rkhamilton/uAlarm/diptrace/uAlarm-audio-PCB.jpg

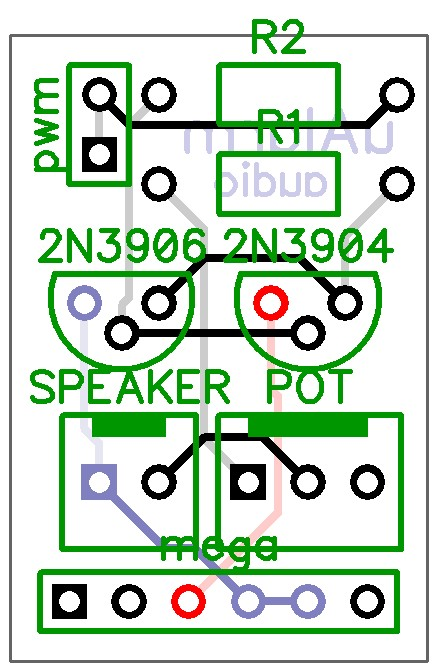
diptrace/uAlarm-audio-PCB.jpg
