rkhamilton/uAlarm/images/glue-detail.jpg

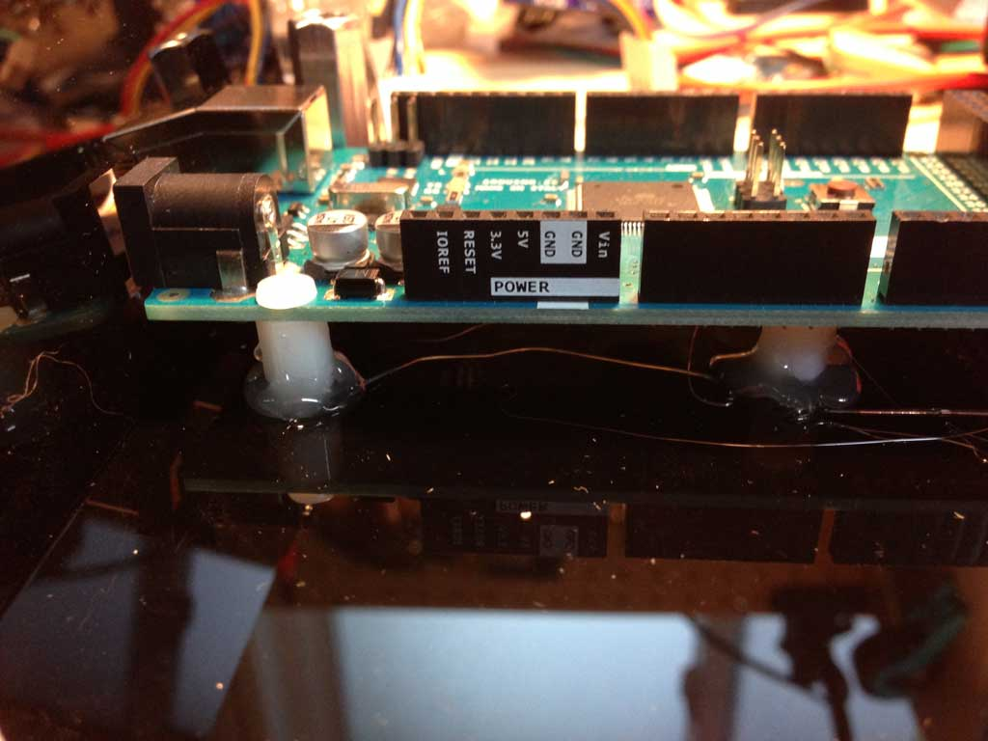
images/glue-detail.jpg
