rkhamilton/uAlarm/images/ponoko-p2.jpg

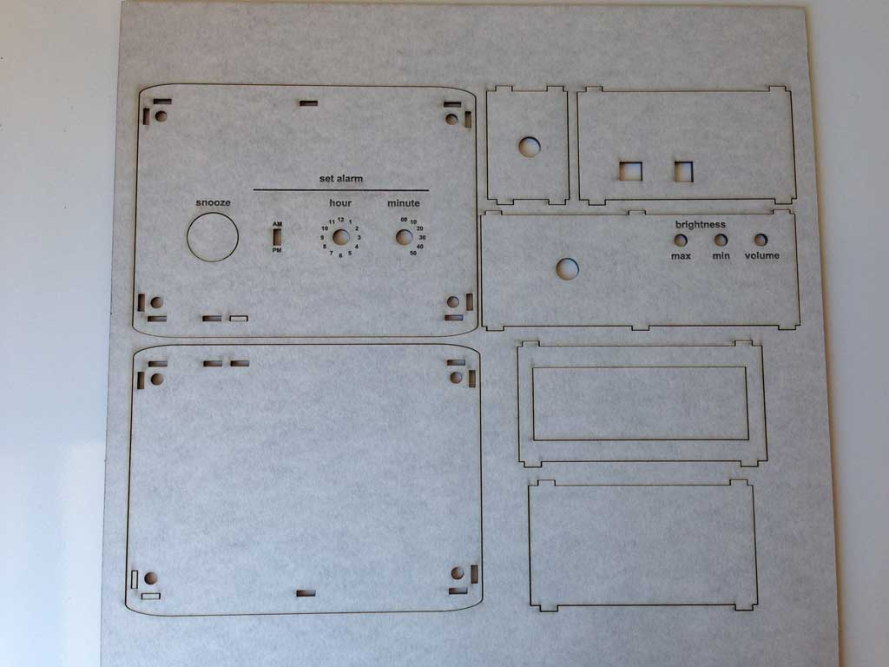
images/ponoko-p2.jpg
