rkhamilton/uAlarm/images/top-angle.jpg

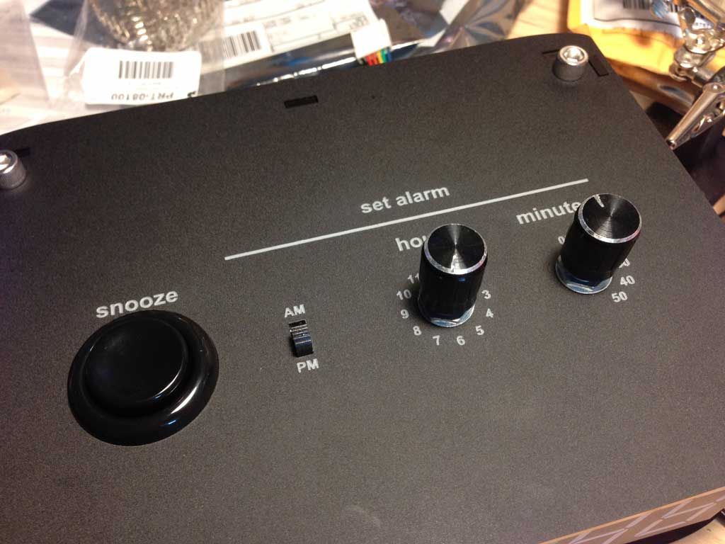
images/top-angle.jpg
