rkhamilton/uAlarm/images/top-plate-from-ponoko.jpg

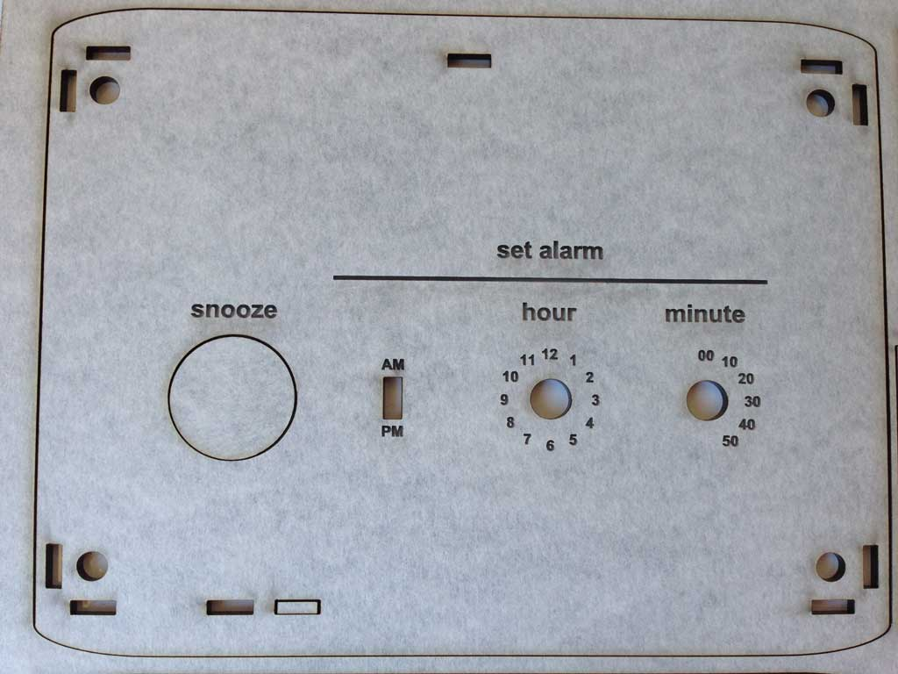
images/top-plate-from-ponoko.jpg
