rkhamilton/uAlarm/images/mock-assembly.jpg

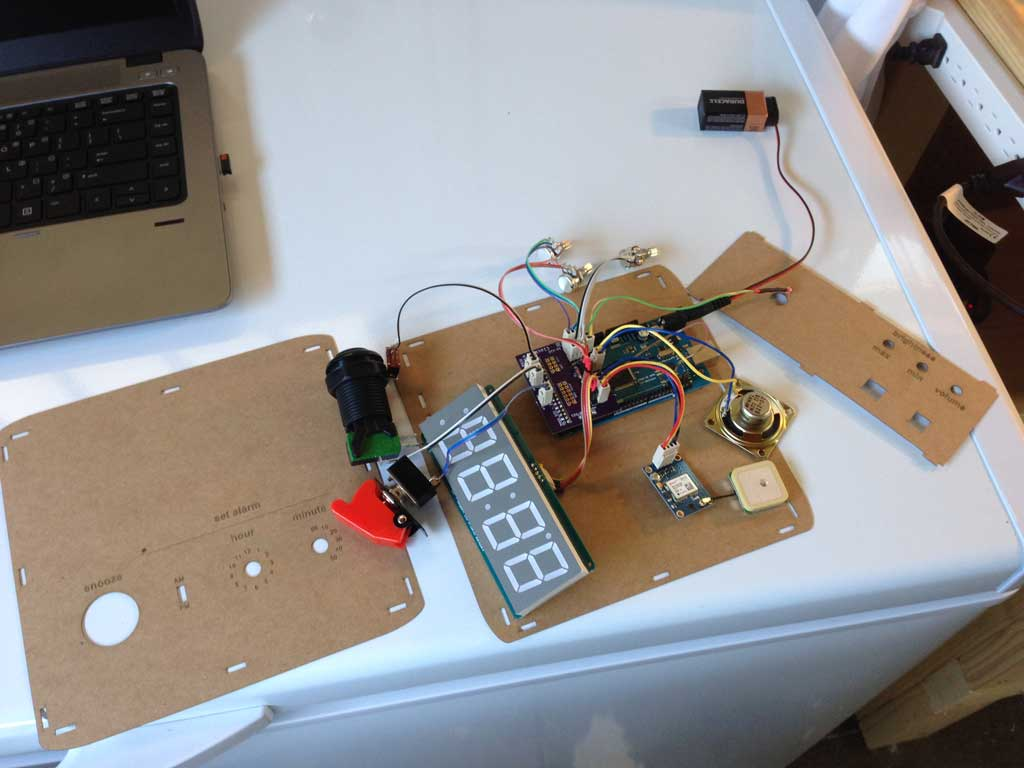
images/mock-assembly.jpg
