rkhamilton/uAlarm/images/rotary-switches-wiring.jpg

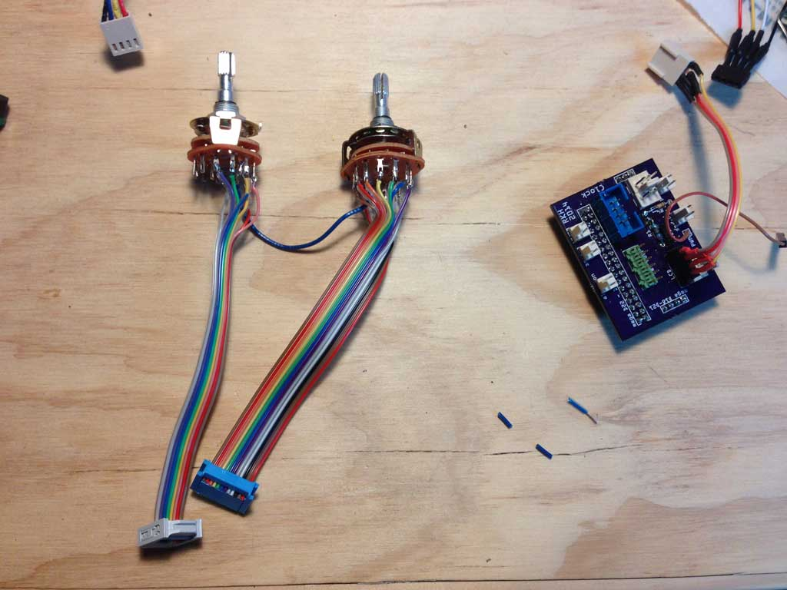
images/rotary-switches-wiring.jpg
