rkhamilton/uAlarm/images/paper-test.jpg

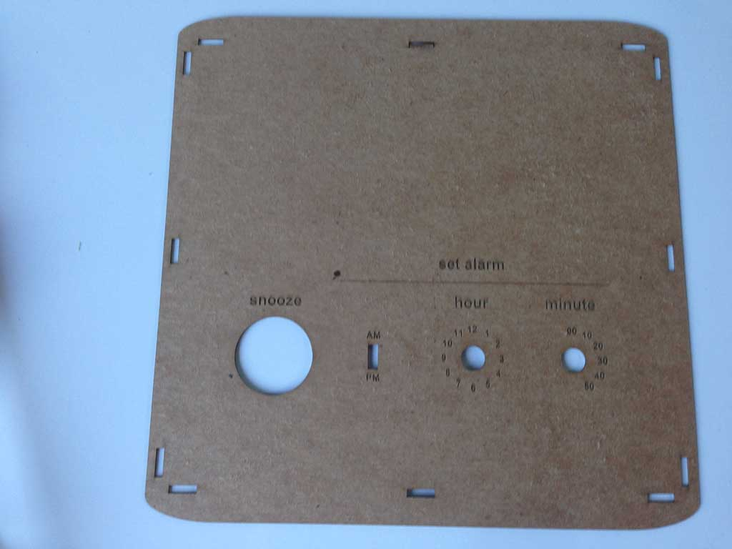
images/paper-test.jpg
